vajicek/semaforky/doc/original_clock_device/IMG_20161114_182417.jpg

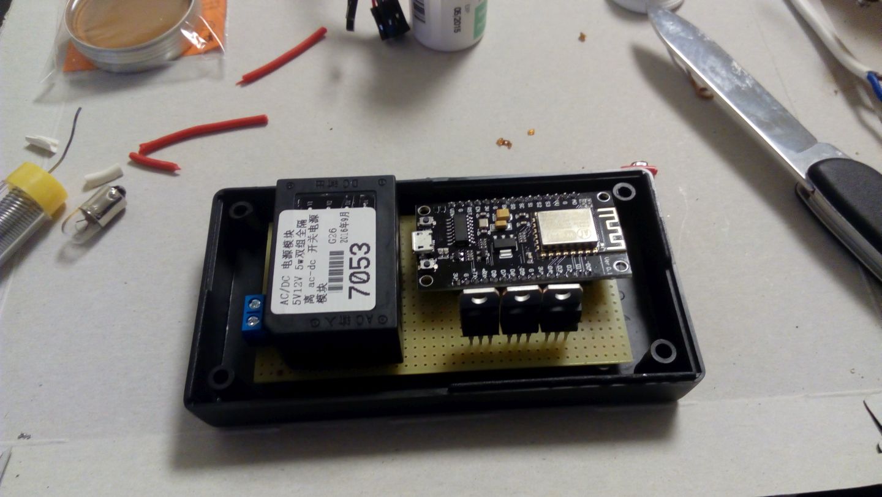
doc/original_clock_device/IMG_20161114_182417.jpg
