vajicek/semaforky/doc/original_clock_device/IMG_20161222_174453.jpg

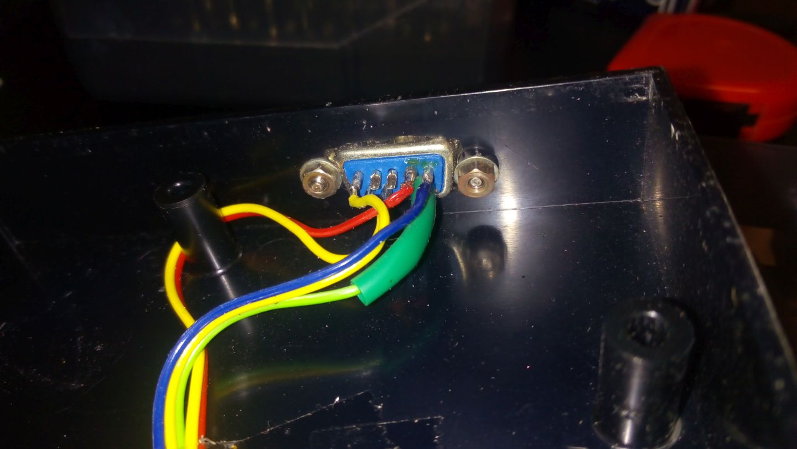
doc/original_clock_device/IMG_20161222_174453.jpg
