vajicek/semaforky/doc/original_clock_device/IMG_20161222_193014.jpg

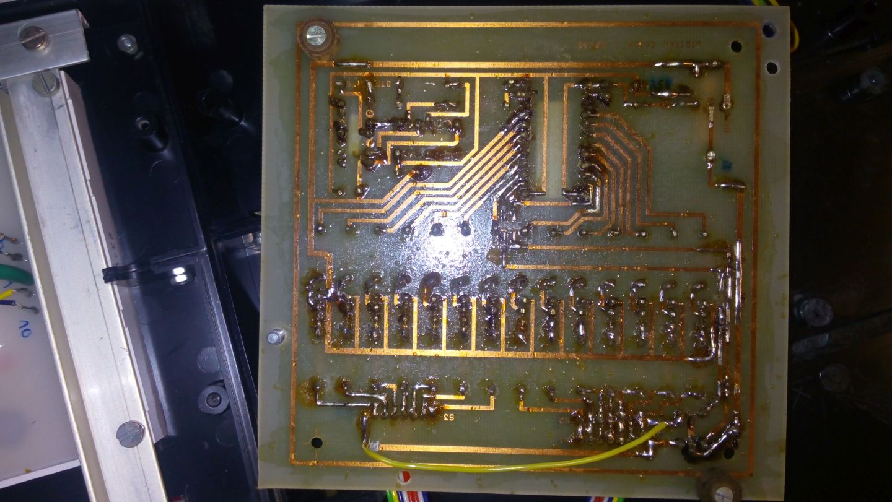
doc/original_clock_device/IMG_20161222_193014.jpg
