vajicek/semaforky/doc/original_semafor/DSC_1394.JPG

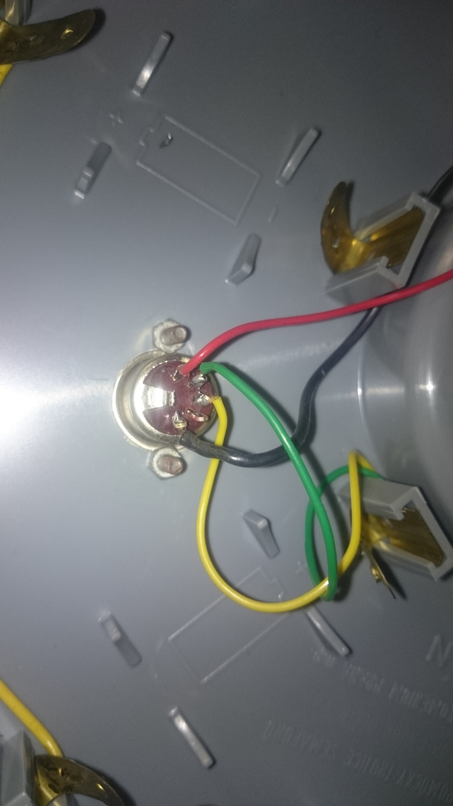
doc/original_semafor/DSC_1394.JPG
