vajicek/semaforky/client/clock_client/clock_client.ino

/// Copyright (C) 2017, Vajsoft
/// Author: Vaclav Krajicek <vajicek@volny.cz>

#include <semaforky_common.h>

SAA1064ClockProcess global;

void setup() {
  global.Init();
  if (!ESPWifiUtils::wifi_disabled) {
    ESPWifiUtils::ConnectWiFiAP();
    ESPWifiUtils::PrintWiFiInfo();
  }
}

void loop() {
  global.Execute();
  delay(100);
}
