vajicek/semaforky/android_app/devices/semaforky_common/semaforky_common.h

/// Copyright (C) 2017, Vajsoft
/// Author: Vaclav Krajicek <vajicek@volny.cz>

#define double_buffer
#include <PxMatrix.h>
#include <Ticker.h>

#include "wifi.h"

#define INVERTED_WIRE_LOGIC
#include "saa1064_i2c.h"

const int SEMAPHORE_CLIENT = 1;
const int CLOCK_CLIENT = 2;
const int SIREN_CLIENT = 3;
const int RGB_MATRIX_DISPLAY_CLIENT = 4;
const int MONO_MATRIX_DISPLAY_CLIENT = 5;

// Wemos D1 mini - common pins
#define POWER_ON_PIN 0
#define CONNECTED_PIN 4

// Ping magic number
#define PING_MAGIC_NUMBER 69

/// data chunk
struct ControlChunk {
  int control;
  int value;
  ControlChunk() : control(0), value(0) {
  }
};

struct RegisterChunk {
  int type;
};

/// Process object, state machine behavior
struct Process {
  WiFiClient client;
  ControlChunk last_chunk;

  /// connect to server specified by global variables
  void ConnectServer();

  /// OnConnectServer event
  virtual void OnConnectServer();

  /// non blocking processing of states
  virtual void Execute();

  /// init output pins and wifi connection
  virtual void Init();

  /// read data chunk
  ControlChunk ReadControlChunk();

  /// handle input
  virtual void Input();

  /// set outputs
  virtual void Output() = 0;

  /// handle ping message
  void HandlePing();

  Process();
};

Process::Process() {
}

ControlChunk Process::ReadControlChunk() {
  Serial.println("ReadControlChunk");
  ControlChunk received_chunk;
  client.read(reinterpret_cast<uint8_t*>(&received_chunk),
    sizeof(received_chunk));
  Serial.print("received_chunk.control=");
  Serial.println(received_chunk.control);
  Serial.print("received_chunk.value=");
  Serial.println(received_chunk.value);
  return received_chunk;
}

void Process::OnConnectServer() {
}

void Process::ConnectServer() {
  Serial.println("Connecting..");
  // starts client connection, checks for connection
  if (client.connect(ESPWifiUtils::servername, ESPWifiUtils::port)) {
    Serial.println("Connected to the server");
    OnConnectServer();
  } else {
    // error message if no client connect
    Serial.println("Connection to the server failed");
  }
}

void Process::HandlePing() {
  Serial.println("Ping received");
  // send pong
  RegisterChunk chunk{PING_MAGIC_NUMBER};
  client.write(reinterpret_cast<uint8_t*>(&chunk),
    sizeof(RegisterChunk));
}

void Process::Input() {
  if (!ESPWifiUtils::wifi_disabled) {
    if (client.connected()) {
      if (client.available()) {
        ControlChunk new_chunk = ReadControlChunk();
        if (new_chunk.control == PING_MAGIC_NUMBER) {
          HandlePing();
        } else {
          last_chunk = new_chunk;
        }
      }
    } else {
      ConnectServer();
    }
  }
}

void Process::Execute() {
  Input();
  Output();
  delay(50);
}

void Process::Init() {
  Serial.begin(115200);

  // wait for serial port to connect. Needed for Leonardo only
  while (!Serial) {
  }

  Serial.println();
  Serial.println("Initialization started");

  if (!ESPWifiUtils::wifi_disabled) {
    ESPWifiUtils::ConnectWiFiAP();
    ESPWifiUtils::PrintWiFiInfo();

    ConnectServer();
  }
}

//-------------------------------------------------------------------------------
// Wemos D1 mini
#define SEMAPHORE_RED_PIN 5
#define SEMAPHORE_YELLOW_PIN 4
#define SEMAPHORE_GREEN_PIN 0

/// Semaphore client specialization.
struct SemaphoreProcess : public Process {
  virtual void Init();
  virtual void Output();
  virtual void OnConnectServer();
};

void SemaphoreProcess::OnConnectServer() {
  RegisterChunk chunk{SEMAPHORE_CLIENT};
  client.write(reinterpret_cast<uint8_t*>(&chunk), sizeof(RegisterChunk));
}

void SemaphoreProcess::Output() {
  digitalWrite(SEMAPHORE_RED_PIN, last_chunk.value == 1 ? HIGH : LOW);
  digitalWrite(SEMAPHORE_YELLOW_PIN, last_chunk.value == 2 ? HIGH : LOW);
  digitalWrite(SEMAPHORE_GREEN_PIN, last_chunk.value == 3 ? HIGH : LOW);
}

void SemaphoreProcess::Init() {
  Process::Init();
  pinMode(SEMAPHORE_RED_PIN, OUTPUT);
  pinMode(SEMAPHORE_YELLOW_PIN, OUTPUT);
  pinMode(SEMAPHORE_GREEN_PIN, OUTPUT);
}

//-------------------------------------------------------------------------------

// Wemos D1 mini
#define SAA1064_CLOCK_CLOCK_PIN 1
#define SAA1064_CLOCK_DATA_PIN 2

void ComputeDigits(int* digits, int digit_count, int value) {
  int divider = 1;
  for (int i = 0; i < digit_count; i++) {
    if (value / divider == 0 && divider > 1) {
      // value is lower than order represented by i-th digit
      // does not apply for 1st order, i.e. if value=0
      digits[digit_count - i - 1] = - 1;
    } else {
      digits[digit_count - i - 1] = (value / divider) % 10;
    }
    divider *= 10;
  }
}

/// Clock client specialization.
struct SAA1064ClockProcess : public Process {
  static const int digit_count = 4;
  SAA1064 saa1064;
  virtual void Init();
  virtual void Output();
  virtual void OnConnectServer();
  SAA1064ClockProcess();
};

SAA1064ClockProcess::SAA1064ClockProcess()
  : saa1064(100, SAA1064_CLOCK_CLOCK_PIN, SAA1064_CLOCK_DATA_PIN) {
}

void SAA1064ClockProcess::OnConnectServer() {
  RegisterChunk chunk{CLOCK_CLIENT};
  client.write(reinterpret_cast<uint8_t*>(&chunk), sizeof(RegisterChunk));
}

void SAA1064ClockProcess::Output() {
  digitalWrite(CONNECTED_PIN, client.connected() ? HIGH : LOW);

  if (last_chunk.value == -1) {
    saa1064.digits(-2, -2, -2, -1);
  } else {
    int digits[4];
    ComputeDigits(digits, digit_count, last_chunk.value);
    saa1064.digits(digits[1], digits[2], digits[3], -1);
  }
}

void SAA1064ClockProcess::Init() {
  // setup common pins
  pinMode(CONNECTED_PIN, OUTPUT);
  pinMode(POWER_ON_PIN, OUTPUT);

  // power on
  digitalWrite(POWER_ON_PIN, HIGH);
  digitalWrite(CONNECTED_PIN, LOW);

  Process::Init();
}

//-------------------------------------------------------------------------------

#define SIREN_TONE_LENGTH 500
#define SIREN_PAUSE_LENGTH 500

// Wemos D1 mini
#define SIREN_AUDIO_PIN 5

/// Clock client specialization.
struct SirenProcess : public Process {
  virtual void Init();
  virtual void Output();
  virtual void OnConnectServer();
};

void SirenProcess::OnConnectServer() {
  RegisterChunk chunk{SIREN_CLIENT};
  client.write(reinterpret_cast<uint8_t*>(&chunk), sizeof(RegisterChunk));
}

void SirenProcess::Output() {
  for (int i = 0; i < last_chunk.value; i++) {
    digitalWrite(SIREN_AUDIO_PIN, HIGH);
    delay(SIREN_TONE_LENGTH);
    digitalWrite(SIREN_AUDIO_PIN, LOW);
    delay(SIREN_PAUSE_LENGTH);
  }
  last_chunk.value = 0;
}

void SirenProcess::Init() {
  Process::Init();
  pinMode(SIREN_AUDIO_PIN, OUTPUT);
}

//-------------------------------------------------------------------------------

static uint16_t color565(uint8_t r, uint8_t g, uint8_t b) {
  return ((b & 0xF8) << 8) | ((g & 0xFC) << 3) | (r >> 3);
}

struct RgbMatrixDisplayProcess : public Process {
  PxMATRIX* display;
  Ticker display_ticker;
  int digit_width;
  int digit_height;
  int digit_size;
  int old_value;
  const uint16_t* colors;
  RgbMatrixDisplayProcess(
    PxMATRIX* display,
    int digit_width,
    int digit_height,
    int digit_size,
    const uint16_t* colors);
  virtual void Init();
  virtual void Output();
  virtual void OnConnectServer();
};

int DecodeTimeValue(int value) {
  return value & 0x0000ffff;
}

int DecodeColorValue(int value) {
  return (value & 0x00ff0000) >> 16;
}

int DecodeBrightnessValue(int value) {
  return (value & 0xff000000) >> 24;
}

RgbMatrixDisplayProcess::RgbMatrixDisplayProcess(
    PxMATRIX* _display,
    int _digit_width,
    int _digit_height,
    int _digit_size,
    const uint16_t* _colors)
    : display(_display),
    digit_width(_digit_width),
    digit_height(_digit_height),
    digit_size(_digit_size),
    old_value(-1),
    colors(_colors) {
    }

void RgbMatrixDisplayProcess::OnConnectServer() {
  RegisterChunk chunk{RGB_MATRIX_DISPLAY_CLIENT};
  client.write(reinterpret_cast<uint8_t*>(&chunk), sizeof(RegisterChunk));
}

void RgbMatrixDisplayProcess::Output() {
  if (old_value == last_chunk.value) {
    return;
  }
  old_value = last_chunk.value;

  display->fillScreen(color565(0, 0, 0));

  auto time = DecodeTimeValue(last_chunk.value);
  auto color = DecodeColorValue(last_chunk.value);
  auto brightness = DecodeBrightnessValue(last_chunk.value);
  display->setBrightness(brightness);

  int digits[4];
  ComputeDigits(digits, 4, time);
  for (int i = 3; i > 0; i--) {
    if (digits[i] >= 0) {
      display->drawChar((i - 1) * digit_width, digit_height,  // coords
        '0' + digits[i],  // character
        colors[color], colors[color],  // colors
        digit_size);  // size
    }
  }
  display->showBuffer();
}

void RgbMatrixDisplayProcess::Init() {
  Process::Init();
  display->begin(8);
  display->clearDisplay();
  display_ticker.attach_ms(4, [this]() {
    this->display->display();
  });
}

//-------------------------------------------------------------------------------

#define P10_LAT 16
#define P10_A 5
#define P10_B 4
#define P10_C 15
#define P10_OE 2

const uint16_t P10_COLORS[] = {
  color565(255, 255, 255),  // white
  color565(255, 0, 0),      // red
  color565(0, 255, 0),      // green
  color565(255, 165, 0)     // orange
};

struct RgbMatrixDisplayProcess32 : public RgbMatrixDisplayProcess {
  PxMATRIX display;
  RgbMatrixDisplayProcess32();
};

RgbMatrixDisplayProcess32::RgbMatrixDisplayProcess32()
  : display(32, 16, P10_LAT, P10_OE, P10_A, P10_B, P10_C),
  RgbMatrixDisplayProcess(&display, 11, 1, 2, P10_COLORS) {
}

//-------------------------------------------------------------------------------

#include "digits_font.h"

#define P5_LAT 16
#define P5_A 5
#define P5_B 4
#define P5_C 15
#define P5_D 12
#define P5_OE 2

const uint16_t P5_COLORS[] = {
  color565(255, 255, 255),  // white
  color565(0, 0, 255),      // red
  color565(0, 255, 0),      // green
  color565(0, 165, 255)     // orange
};

struct RgbMatrixDisplayProcess64 : public RgbMatrixDisplayProcess {
  PxMATRIX display;
  RgbMatrixDisplayProcess64();
  virtual void Init();
};

RgbMatrixDisplayProcess64::RgbMatrixDisplayProcess64()
  : display(64, 32, P5_LAT, P5_OE, P5_A, P5_B, P5_C, P5_D),
  RgbMatrixDisplayProcess(&display, 21, 32, 1, P5_COLORS) {
}

void RgbMatrixDisplayProcess64::Init() {
  RgbMatrixDisplayProcess::Init();
  display.setFont(&FixedWidthDigit);
  display.setTextWrap(false);
}

//-------------------------------------------------------------------------------

#include <SPI.h>
#include <DMD2.h>
#include "digits32.h"

/* P10 led pannel pins to ESP 8266
A D0      2     16
B D6      4     12
CLK D5    8     14
SCK D3    10    0
R D7      12    13
NOE D8    1     15
GND GND   3     g
*/

struct MySPIDMD : public SPIDMD {
  MySPIDMD(byte panelsWide, byte panelsHigh) :
    SPIDMD(panelsWide, panelsHigh) {
  }

  void setPixel(unsigned int x1, unsigned int y1, DMDGraphicsMode mode) {
    unsigned int x, y;
    map_panel_coords(x1, y1, &x, &y);
    SPIDMD::setPixel(x, y, mode);
  }

  void map_panel_coords(unsigned int x, unsigned int y,
                        unsigned int* tx, unsigned int* ty) {
    const int PANEL_H = 16;
    const int PANEL_W = 32;
    const int PANELS = 3;
    const int MAX_X = PANEL_H * PANELS - 1;

    int panel = (MAX_X - x) / PANEL_H;
    *tx = (PANELS - 1) * PANEL_W - (PANELS - 1 - panel) * PANEL_W + y;
    *ty = PANEL_H - 1 - x % PANEL_H;
  }
};

struct MonoMatrixDisplayProcess : public Process {
  MySPIDMD dmd;
  MySPIDMD buffer;
  int old_value;
  unsigned long last_time;
  MonoMatrixDisplayProcess();
  virtual void Init();
  virtual void Output();
  virtual void OnConnectServer();
  virtual void Execute();
  void DrawDigits();
};

MonoMatrixDisplayProcess::MonoMatrixDisplayProcess()
    : dmd(3, 1), buffer(3, 1), old_value(-1), last_time(0) {
}

void MonoMatrixDisplayProcess::OnConnectServer() {
  RegisterChunk chunk{MONO_MATRIX_DISPLAY_CLIENT};
  client.write(reinterpret_cast<uint8_t*>(&chunk), sizeof(RegisterChunk));
}

void MonoMatrixDisplayProcess::DrawDigits() {
  auto time = DecodeTimeValue(last_chunk.value);
  auto color = DecodeColorValue(last_chunk.value);
  auto brightness = DecodeBrightnessValue(last_chunk.value);

  buffer.fillScreen(false);

  int digits[4];
  ComputeDigits(digits, 4, time);
  for (int i = 3; i > 0; i--) {
    if (digits[i] >= 0) {
      buffer.drawChar((i - 1) * 16, 0, '0' + digits[i], GRAPHICS_ON, Digits32);
    }
  }

  dmd.swapBuffers(buffer);
  dmd.setBrightness(brightness);
}

void MonoMatrixDisplayProcess::Output() {
  if (old_value != last_chunk.value) {
    old_value = last_chunk.value;
    DrawDigits();
  }
  dmd.scanDisplay();
}

void MonoMatrixDisplayProcess::Init() {
  Process::Init();
  dmd.beginNoTimer();
}

void MonoMatrixDisplayProcess::Execute() {
  unsigned long current = millis();
  if ((current - last_time) > 50) {
    last_time = current;
    Input();
  }
  Output();
}
