vajicek/semaforky/web_app/devices/semaforky_webui_common/semaforky_webui_common_esp32.h

/// Copyright (C) 2026, Vajsoft
/// Author: Vaclav Krajicek <vajicek@volny.cz>

#include "semaforky_webui_common.h"

#include "digits32_font.h"
#include "abcd32_font.h"

class P10x3 : public Base {
private:
	FthnLabsDisplay display;
	GFXcanvas1 canvas;
	TaskHandle_t displayTaskHandle = NULL;

	int oldValue = -1;

	void updateDisplay();
	void drawDigits();
	void drawLetters();
	void copyCanvas();

public:
	void redrawDisplay();

	void Init();
	void Execute();

	FthnLabsDisplay* getDisplay();

	P10x3(BaseSettings *baseSettings);
};

void P10x3::drawDigits() {
	auto time = decodeTimeValue(value);
	auto brightness = decodeBrightnessValue(value);

	canvas.fillScreen(0);
	canvas.setFont(&FixedWidthDigit);

	int digits[4];
	computeDigits(digits, 4, time);
	for (int i = 3; i > 0; i--) {
		if (digits[i] >= 0) {
			canvas.drawChar(2 + (i - 1) * 16, 32, '0' + digits[i], 0xFFFF, 0, 1);
		}
	}

	display.setBrightness(brightness);
	copyCanvas();
	display.display();
}

void P10x3::drawLetters() {
	canvas.fillScreen(0);
	canvas.setFont(&FixedWidthAbcd);

	if (value == 1) {
		canvas.drawChar(0, 32, 'A', 0xFFFF, 0, 1);
		canvas.drawChar(24, 32, 'B', 0xFFFF, 0, 1);
	} else if (value == 2) {
		canvas.drawChar(0, 32, 'C', 0xFFFF, 0, 1);
		canvas.drawChar(24, 32, 'D', 0xFFFF, 0, 1);
	}

	copyCanvas();
	display.display();
}

void P10x3::copyCanvas() {
	for (int16_t y = 0; y < 32; y++) {
		for (int16_t x = 0; x < 48; x++) {
			bool pixelOn = canvas.getPixel(x, y);
			uint16_t colorToDraw = pixelOn ? 0xFFFF : 0x0;
			display.drawPixel(y, 48 - x, colorToDraw);
		}
	}
}

void P10x3::updateDisplay() {
	if (controlValue == CONTROL_VALUE_LINES) {
		if (oldValue != value) {
			oldValue = value;
			drawLetters();
		}
	} else if (controlValue == CONTROL_VALUE_CLOCK) {
		if (oldValue != value) {
			oldValue = value;
			drawDigits();
		}
	}
}

void P10x3::redrawDisplay() {
}

void displayUpdateLoop(void *pvParameters) {
	for (;;) {
		((P10x3 *)pvParameters)->getDisplay()->loop();
		vTaskDelay(1 / portTICK_PERIOD_MS);
	}
}

void P10x3::Init() {
	Base::Init();
	display.begin();

	// Create the display task on Core 1
	xTaskCreatePinnedToCore(
		displayUpdateLoop,  // Function to implement the task
		"DisplayTask",      // Name of the task
		4096,               // Stack size in words
		this,               // Task input parameter
		1,                  // Priority of the task
		&displayTaskHandle, // Task handle
		1                   // Core where the task should run (Core 1)
	);
}

void P10x3::Execute() {
	Base::Execute();
	updateDisplay();
	redrawDisplay();
}

DisplayConfig getP10x3DisplayConfig() {
	uint8_t oePin = 22;
	uint8_t clkPin = 18;
	uint8_t latPin = 2;
	uint8_t aPin = 19;
	uint8_t bPin = 21;
	uint8_t rDataPin = 23;

	uint8_t panelWidth = 32;
	uint8_t panelHeight = 48;

	// address pins
	static uint8_t addressPins[] = {aPin, bPin};

	// data pins
	static uint8_t dataPins[] = {rDataPin};

	DisplayConfig cfg = {
		panelWidth, panelHeight, // panel
		oePin, clkPin, latPin,   // control
		addressPins, 2,          // address
		dataPins, 1              // data
	};
	return cfg;
}

FthnLabsDisplay* P10x3::getDisplay() {
	return &display;
}

P10x3::P10x3(BaseSettings *baseSettings)
	: Base(baseSettings), display(getP10x3DisplayConfig()), canvas(48, 32) {}
