vajicek/semaforky/android_app/devices/semaforky_common/digits_font.h

/// Copyright (C) 2023, Vajsoft
/// Author: Vaclav Krajicek <vajicek@volny.cz>

const uint8_t FixedWidthDigitBitmaps[] PROGMEM = {
	// 'digit0, 21x32px
	0x00, 0x00, 0x00, 0x00, 0xfc, 0x00, 0x03, 0xff, 0x00, 0x07, 0xff, 0x80, 0x0f, 0x87, 0xc0, 0x1e,
	0x03, 0xe0, 0x1e, 0x01, 0xe0, 0x3c, 0x00, 0xf0, 0x3c, 0x00, 0xf0, 0x3c, 0x00, 0xf0, 0x78, 0x00,
	0x78, 0x78, 0x00, 0x78, 0x78, 0x00, 0x78, 0x78, 0x00, 0x78, 0x78, 0x00, 0x78, 0x78, 0x00, 0x78,
	0x78, 0x00, 0x78, 0x78, 0x00, 0x78, 0x78, 0x00, 0x78, 0x78, 0x00, 0x78, 0x78, 0x00, 0x78, 0x78,
	0x00, 0x78, 0x3c, 0x00, 0xf0, 0x3c, 0x00, 0xf0, 0x3c, 0x00, 0xf0, 0x1e, 0x01, 0xe0, 0x1e, 0x03,
	0xe0, 0x0f, 0x87, 0xc0, 0x07, 0xff, 0x80, 0x03, 0xff, 0x00, 0x00, 0xfc, 0x00, 0x00, 0x00, 0x00,

	// 'digit1, 21x32px
	0x00, 0x00, 0x00, 0x00, 0x00, 0x00, 0x07, 0xf8, 0x00, 0x3f, 0xf8, 0x00, 0x3f, 0xf8, 0x00, 0x3c,
	0x78, 0x00, 0x00, 0x78, 0x00, 0x00, 0x78, 0x00, 0x00, 0x78, 0x00, 0x00, 0x78, 0x00, 0x00, 0x78,
	0x00, 0x00, 0x78, 0x00, 0x00, 0x78, 0x00, 0x00, 0x78, 0x00, 0x00, 0x78, 0x00, 0x00, 0x78, 0x00,
	0x00, 0x78, 0x00, 0x00, 0x78, 0x00, 0x00, 0x78, 0x00, 0x00, 0x78, 0x00, 0x00, 0x78, 0x00, 0x00,
	0x78, 0x00, 0x00, 0x78, 0x00, 0x00, 0x78, 0x00, 0x00, 0x78, 0x00, 0x00, 0x78, 0x00, 0x00, 0x78,
	0x00, 0x00, 0x78, 0x00, 0x1f, 0xff, 0xe0, 0x1f, 0xff, 0xe0, 0x1f, 0xff, 0xe0, 0x00, 0x00, 0x00,

	// 'digit2, 21x32px
	0x00, 0x00, 0x00, 0x07, 0xf8, 0x00, 0x3f, 0xfe, 0x00, 0x7f, 0xff, 0x80, 0x7c, 0x0f, 0x80, 0x70,
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
	{7*96, 24, 32, 21, 0, -32},   // 0x37 '7'
	{8*96, 24, 32, 21, 0, -32},   // 0x38 '8'
	{9*96, 24, 32, 21, 0, -32},   // 0x39 '9'
};

const GFXfont FixedWidthDigit PROGMEM = {
	(uint8_t *)FixedWidthDigitBitmaps,
	(GFXglyph *)FixedWidthDigitGlyphs,
	0x30, 0x39, 32
};
