vajicek/semaforky/web_app/devices/semaforky_webui_common/digits32_font.h

/// Copyright (C) 2023, Vajsoft
/// Author: Vaclav Krajicek <vajicek@volny.cz>

const uint8_t FixedWidthDigitBitmaps[] PROGMEM = {
0x0F, 0xC0, 0xFF, 0xC7, 0xFF, 0x9F, 0xFE, 0xF8, 0x7F, 0xC0, 0xFF, 0x03, 0xFC, 0x0F, 0xF0, 0x3F, 0xC0, 0xFF, 0x07, 0xFC, 0x1F, 0xF0, 0xFF, 0xC3, 0xFF, 0x1F, 0xFC, 0xEF, 0xF7, 0x3F, 0xF8, 0xFF, 0xC3, 0xFF, 0x0F, 0xF8, 0x3F, 0xE0, 0xFF, 0x03, 0xFC, 0x0F, 0xF0, 0x3F, 0xC0, 0xFF, 0x03, 0xFE, 0x1F, 0x7F, 0xF9, 0xFF, 0xE3, 0xFF, 0x03, 0xF0,
0x03, 0xF0, 0x1F, 0xE0, 0xFF, 0x87, 0xFE, 0x3F, 0xF9, 0xFF, 0xEF, 0xFF, 0xBF, 0x3E, 0x70, 0xF8, 0x03, 0xE0, 0x0F, 0x80, 0x3E, 0x00, 0xF8, 0x03, 0xE0, 0x0F, 0x80, 0x3E, 0x00, 0xF8, 0x03, 0xE0, 0x0F, 0x80, 0x3E, 0x00, 0xF8, 0x03, 0xE0, 0x0F, 0x80, 0x3E, 0x00, 0xF8, 0x03, 0xE0, 0x0F, 0x80, 0x3E, 0x00, 0xF8, 0x03, 0xE0, 0x0F, 0x80, 0x1C,
0x0F, 0xE0, 0x7F, 0xE3, 0xFF, 0x9F, 0xFF, 0xFF, 0xFF, 0xE1, 0xFF, 0x03, 0xD8, 0x0F, 0x00, 0x3C, 0x00, 0xF0, 0x03, 0xC0, 0x1F, 0x00, 0x7C, 0x03, 0xF0, 0x1F, 0xC0, 0xFE, 0x07, 0xF0, 0x3F, 0x81, 0xFC, 0x0F, 0xE0, 0x7F, 0x01, 0xF8, 0x0F, 0xC0, 0x3F, 0x00, 0xF8, 0x03, 0xE0, 0x0F, 0x80, 0x3E, 0x00, 0xFF, 0xFB, 0xFF, 0xFF, 0xFF, 0xDF, 0xFE,
0x0F, 0xC0, 0xFF, 0xC7, 0xFF, 0x9F, 0xFE, 0xF8, 0x7F, 0xC0, 0xF6, 0x03, 0xC0, 0x0F, 0x00, 0x3C, 0x00, 0xF0, 0x03, 0xC0, 0x0F, 0x00, 0x3C, 0x01, 0xE0, 0x3F, 0x81, 0xFC, 0x07, 0xF0, 0x0F, 0xE0, 0x07, 0x80, 0x0F, 0x00, 0x3C, 0x00, 0xF0, 0x03, 0xC0, 0x0F, 0x00, 0x3D, 0x80, 0xFF, 0x03, 0xFE, 0x1F, 0x7F, 0xF9, 0xFF, 0xE3, 0xFF, 0x03, 0xF0,
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
{8 * 56, 14, 32, 15, 0, -32}, // 0x38 '8'
{9 * 56, 14, 32, 15, 0, -32}, // 0x39 '9'
};

const GFXfont FixedWidthDigit PROGMEM = {(uint8_t *)FixedWidthDigitBitmaps,
                                         (GFXglyph *)FixedWidthDigitGlyphs,
                                         0x30, 0x39, 32};
