vajicek/semaforky/web_app/devices/semaforky_webui_common/digits32.h

#include <inttypes.h>
#ifdef __AVR__
#include <avr/pgmspace.h>
#elif defined (ESP8266)
#include <pgmspace.h>
#else
#define PROGMEM
#endif

#ifndef DIGITS_32_H
#define DIGITS_32_H

static const uint8_t Digits32[] PROGMEM = {
      0x42, 0x02, // total size of this array
      14, // width (may vary)
      32, // height
      48, // first char
      10, // char count

      // char widths
      // for each character the separate width in pixels
      14, 14, 14, 14, 14, 14, 14, 14, 14, 14,

      // font data
      // bit field of all characters
      0xF0, 0xFC, 0xFE, 0xFE, 0x1F, 0x0F, 0x0F, 0x0F, 0x0F, 0x1F, 0xFE, 0xFE, 0xFC, 0xF0, 0xFF, 0xFF, 0xFF, 0xFF, 0x00, 0x00, 0x80, 0xC0, 0xF0, 0x7C, 0xFF, 0xFF, 0xFF, 0xFF, 0xFF, 0xFF, 0xFF, 0xFF, 0x3E, 0x0F, 0x03, 0x01, 0x00, 0x00, 0xFF, 0xFF, 0xFF, 0xFF, 0x0F, 0x3F, 0x7F, 0x7F, 0xF8, 0xF0, 0xF0, 0xF0, 0xF0, 0xF8, 0x7F, 0x7F, 0x3F, 0x0F, // 48
      0xC0, 0xE0, 0xF0, 0xF8, 0xFC, 0xFE, 0x7F, 0x7F, 0xFF, 0xFF, 0xFF, 0xFF, 0xFE, 0x00, 0x00, 0x01, 0x01, 0x01, 0x00, 0x00, 0x00, 0x00, 0xFF, 0xFF, 0xFF, 0xFF, 0xFF, 0x00, 0x00, 0x00, 0x00, 0x00, 0x00, 0x00, 0x00, 0x00, 0xFF, 0xFF, 0xFF, 0xFF, 0xFF, 0x00, 0x00, 0x00, 0x00, 0x00, 0x00, 0x00, 0x00, 0x00, 0x7F, 0xFF, 0xFF, 0xFF, 0x7F, 0x00, // 49
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
};

#endif
