vajicek/semaforky/web_app/devices/semaforky_webui_common/abcd32_font.h

/// Copyright (C) 2024, Vajsoft
/// Author: Vaclav Krajicek <vajicek@volny.cz>

const uint8_t FixedWidthAbcdBitmaps[] PROGMEM = {
0x00, 0x00, 0x00, 0x00, 0x7E, 0x00, 0x00, 0x7E, 0x00, 0x00, 0x7E, 0x00, 0x00, 0xFF, 0x00, 0x00, 0xFF, 0x00, 0x00, 0xFF, 0x00, 0x01, 0xFF, 0x80, 0x01, 0xFF, 0x80, 0x01, 0xFF, 0x80, 0x03, 0xFF, 0xC0, 0x03, 0xE7, 0xC0, 0x03, 0xE7, 0xC0, 0x07, 0xE7, 0xC0, 0x07, 0xE7, 0xE0, 0x07, 0xC3, 0xE0, 0x07, 0xC3, 0xE0, 0x0F, 0xC3, 0xF0, 0x0F, 0xC3, 0xF0, 0x0F, 0x83, 0xF0, 0x1F, 0xFF, 0xF8, 0x1F, 0xFF, 0xF8, 0x1F, 0xFF, 0xF8, 0x3F, 0xFF, 0xFC, 0x3F, 0x00, 0xFC, 0x3F, 0x00, 0xFC, 0x7E, 0x00, 0x7C, 0x7E, 0x00, 0x7E, 0x7E, 0x00, 0x7E, 0x7E, 0x00, 0x7E, 0x00, 0x00, 0x00, 0x00, 0x00, 0x00,
0x00, 0x00, 0x00, 0x1F, 0xFF, 0x00, 0x1F, 0xFF, 0xC0, 0x1F, 0xFF, 0xE0, 0x1F, 0xFF, 0xF0, 0x1F, 0x83, 0xF0, 0x1F, 0x81, 0xF8, 0x1F, 0x81, 0xF8, 0x1F, 0x81, 0xF8, 0x1F, 0x81, 0xF8, 0x1F, 0x81, 0xF8, 0x1F, 0x81, 0xF0, 0x1F, 0x83, 0xF0, 0x1F, 0xFF, 0xE0, 0x1F, 0xFF, 0xC0, 0x1F, 0xFF, 0xC0, 0x1F, 0xFF, 0xF0, 0x1F, 0x83, 0xF0, 0x1F, 0x81, 0xF8, 0x1F, 0x81, 0xF8, 0x1F, 0x81, 0xF8, 0x1F, 0x81, 0xF8, 0x1F, 0x81, 0xF8, 0x1F, 0x81, 0xF8, 0x1F, 0x83, 0xF8, 0x1F, 0x83, 0xF0, 0x1F, 0xFF, 0xF0, 0x1F, 0xFF, 0xE0, 0x1F, 0xFF, 0xC0, 0x1F, 0xFF, 0x00, 0x00, 0x00, 0x00, 0x00, 0x00, 0x00,
0x00, 0x00, 0x00, 0x00, 0x7F, 0x00, 0x01, 0xFF, 0xC0, 0x07, 0xFF, 0xF0, 0x0F, 0xFF, 0xF0, 0x0F, 0xC3, 0xF8, 0x1F, 0x81, 0xF8, 0x1F, 0x80, 0xFC, 0x1F, 0x00, 0xFC, 0x3F, 0x00, 0xFC, 0x3F, 0x00, 0xFC, 0x3F, 0x00, 0x00, 0x3F, 0x00, 0x00, 0x3F, 0x00, 0x00, 0x3F, 0x00, 0x00, 0x3F, 0x00, 0x00, 0x3F, 0x00, 0x00, 0x3F, 0x00, 0x00, 0x3F, 0x00, 0x00, 0x3F, 0x00, 0x00, 0x3F, 0x00, 0x00, 0x3F, 0x00, 0xFC, 0x3F, 0x00, 0xFC, 0x1F, 0x80, 0xFC, 0x1F, 0x81, 0xF8, 0x0F, 0xC3, 0xF8, 0x0F, 0xFF, 0xF0, 0x07, 0xFF, 0xE0, 0x03, 0xFF, 0xC0, 0x00, 0x7F, 0x00, 0x00, 0x00, 0x00, 0x00, 0x00, 0x00,
0x00, 0x00, 0x00, 0x1F, 0xFC, 0x00, 0x1F, 0xFF, 0x80, 0x1F, 0xFF, 0xC0, 0x1F, 0xFF, 0xE0, 0x1F, 0x87, 0xF0, 0x1F, 0x81, 0xF8, 0x1F, 0x81, 0xF8, 0x1F, 0x80, 0xF8, 0x1F, 0x80, 0xFC, 0x1F, 0x80, 0xFC, 0x1F, 0x80, 0xFC, 0x1F, 0x80, 0xFC, 0x1F, 0x80, 0xFC, 0x1F, 0x80, 0xFC, 0x1F, 0x80, 0xFC, 0x1F, 0x80, 0xFC, 0x1F, 0x80, 0xFC, 0x1F, 0x80, 0xFC, 0x1F, 0x80, 0xFC, 0x1F, 0x80, 0xFC, 0x1F, 0x80, 0xFC, 0x1F, 0x80, 0xF8, 0x1F, 0x81, 0xF8, 0x1F, 0x81, 0xF8, 0x1F, 0x87, 0xF0, 0x1F, 0xFF, 0xE0, 0x1F, 0xFF, 0xC0, 0x1F, 0xFF, 0x80, 0x1F, 0xFC, 0x00, 0x00, 0x00, 0x00, 0x00, 0x00, 0x00
};

const GFXglyph FixedWidthAbcdGlyphs[] PROGMEM = {
	// Index,  W, H, xAdv, dX, dY
	{0*96, 24, 32, 22, 0, -32},   // 0x41 'A'
	{1*96, 24, 32, 22, 0, -32},   // 0x42 'B'
	{2*96, 24, 32, 22, 0, -32},   // 0x43 'C'
	{3*96, 24, 32, 22, 0, -32},   // 0x44 'D'
};

const GFXfont FixedWidthAbcd PROGMEM = {
	(uint8_t *)FixedWidthAbcdBitmaps,
	(GFXglyph *)FixedWidthAbcdGlyphs,
	0x41, 0x44, 32
};
