vajicek/semaforky/web_app/devices/semaforky_webui_common/abcd32.h

#include <inttypes.h>
#ifdef __AVR__
#include <avr/pgmspace.h>
#elif defined (ESP8266)
#include <pgmspace.h>
#else
#define PROGMEM
#endif

#ifndef ABCD_32_H
#define ABCD_32_H

static const uint8_t Abcd32[] PROGMEM = {
      0x42, 0x02, // total size of this array
      24, // width (may vary)
      32, // height
      65, // first char
      4,  // char count

      // char widths
      // for each character the separate width in pixels
      24, 24, 24, 24,

      // font data
      // bit field of all characters
      0x00, 0x00, 0x00, 0x00, 0x00, 0x00, 0x00, 0x80, 0xf0, 0xfe, 0xfe, 0xfe, 0xfe, 0xfe, 0xfe, 0xf0, 0x80, 0x00, 0x00, 0x00, 0x00, 0x00, 0x00, 0x00, 0x00, 0x00, 0x00, 0x00, 0x00, 0xe0, 0xfc, 0xff, 0xff, 0xff, 0x7f, 0x07, 0x07, 0x7f, 0xff, 0xff, 0xff, 0xfc, 0xc0, 0x00, 0x00, 0x00, 0x00, 0x00, 0x00, 0x00, 0x80, 0xf0, 0xfe, 0xff, 0xff, 0xff, 0xff, 0xf7, 0xf0, 0xf0, 0xf0, 0xf0, 0xff, 0xff, 0xff, 0xff, 0xff, 0xfe, 0xf0, 0x80, 0x00, 0x00, 0x00, 0x3c, 0x3f, 0x3f, 0x3f, 0x3f, 0x3f, 0x03, 0x00, 0x00, 0x00, 0x00, 0x00, 0x00, 0x00, 0x00, 0x03, 0x3f, 0x3f, 0x3f, 0x3f, 0x3f, 0x38, 0x00, //A
      0x00, 0x00, 0x00, 0xfe, 0xfe, 0xfe, 0xfe, 0xfe, 0xfe, 0x1e, 0x1e, 0x1e, 0x1e, 0x1e, 0x3e, 0xfe, 0xfc, 0xfc, 0xf8, 0xf0, 0xc0, 0x00, 0x00, 0x00, 0x00, 0x00, 0x00, 0xff, 0xff, 0xff, 0xff, 0xff, 0xff, 0xe0, 0xe0, 0xe0, 0xe0, 0xe0, 0xf0, 0xff, 0xff, 0xff, 0x3f, 0x1f, 0x07, 0x00, 0x00, 0x00, 0x00, 0x00, 0x00, 0xff, 0xff, 0xff, 0xff, 0xff, 0xff, 0x01, 0x01, 0x01, 0x01, 0x01, 0x03, 0xff, 0xff, 0xff, 0xff, 0xff, 0xfc, 0x00, 0x00, 0x00, 0x00, 0x00, 0x00, 0x3f, 0x3f, 0x3f, 0x3f, 0x3f, 0x3f, 0x3c, 0x3c, 0x3c, 0x3c, 0x3c, 0x3f, 0x3f, 0x1f, 0x1f, 0x0f, 0x07, 0x01, 0x00, 0x00, 0x00, //B
      0x00, 0x00, 0x00, 0xc0, 0xf0, 0xf8, 0xf8, 0xfc, 0xfc, 0x3e, 0x1e, 0x1e, 0x1e, 0x1e, 0x3e, 0x7e, 0xfc, 0xfc, 0xf8, 0xf8, 0xe0, 0x80, 0x00, 0x00, 0x00, 0x00, 0xfe, 0xff, 0xff, 0xff, 0xff, 0xff, 0x00, 0x00, 0x00, 0x00, 0x00, 0x00, 0x00, 0x00, 0x07, 0x07, 0x07, 0x07, 0x07, 0x07, 0x00, 0x00, 0x00, 0x00, 0x7f, 0xff, 0xff, 0xff, 0xff, 0xff, 0x80, 0x00, 0x00, 0x00, 0x00, 0x00, 0x00, 0x00, 0xe0, 0xe0, 0xe0, 0xe0, 0xe0, 0xe0, 0x00, 0x00, 0x00, 0x00, 0x00, 0x01, 0x07, 0x0f, 0x1f, 0x1f, 0x1f, 0x3e, 0x3c, 0x3c, 0x3c, 0x3c, 0x3e, 0x3f, 0x1f, 0x1f, 0x0f, 0x07, 0x03, 0x00, 0x00, 0x00, //C
      0x00, 0x00, 0x00, 0xfe, 0xfe, 0xfe, 0xfe, 0xfe, 0xfe, 0x1e, 0x1e, 0x1e, 0x1e, 0x3e, 0x3c, 0xfc, 0xfc, 0xf8, 0xf0, 0xe0, 0xc0, 0x00, 0x00, 0x00, 0x00, 0x00, 0x00, 0xff, 0xff, 0xff, 0xff, 0xff, 0xff, 0x00, 0x00, 0x00, 0x00, 0x00, 0x00, 0x00, 0xff, 0xff, 0xff, 0xff, 0xff, 0xfe, 0x00, 0x00, 0x00, 0x00, 0x00, 0xff, 0xff, 0xff, 0xff, 0xff, 0xff, 0x00, 0x00, 0x00, 0x00, 0x00, 0x00, 0x80, 0xff, 0xff, 0xff, 0xff, 0xff, 0x3f, 0x00, 0x00, 0x00, 0x00, 0x00, 0x3f, 0x3f, 0x3f, 0x3f, 0x3f, 0x3f, 0x3c, 0x3c, 0x3c, 0x3c, 0x3e, 0x1e, 0x1f, 0x1f, 0x0f, 0x07, 0x03, 0x01, 0x00, 0x00, 0x00, //D
};

#endif
